hasithperera/APRS_tracker/data/aprs_v3_diagnostics/SCR01.PNG

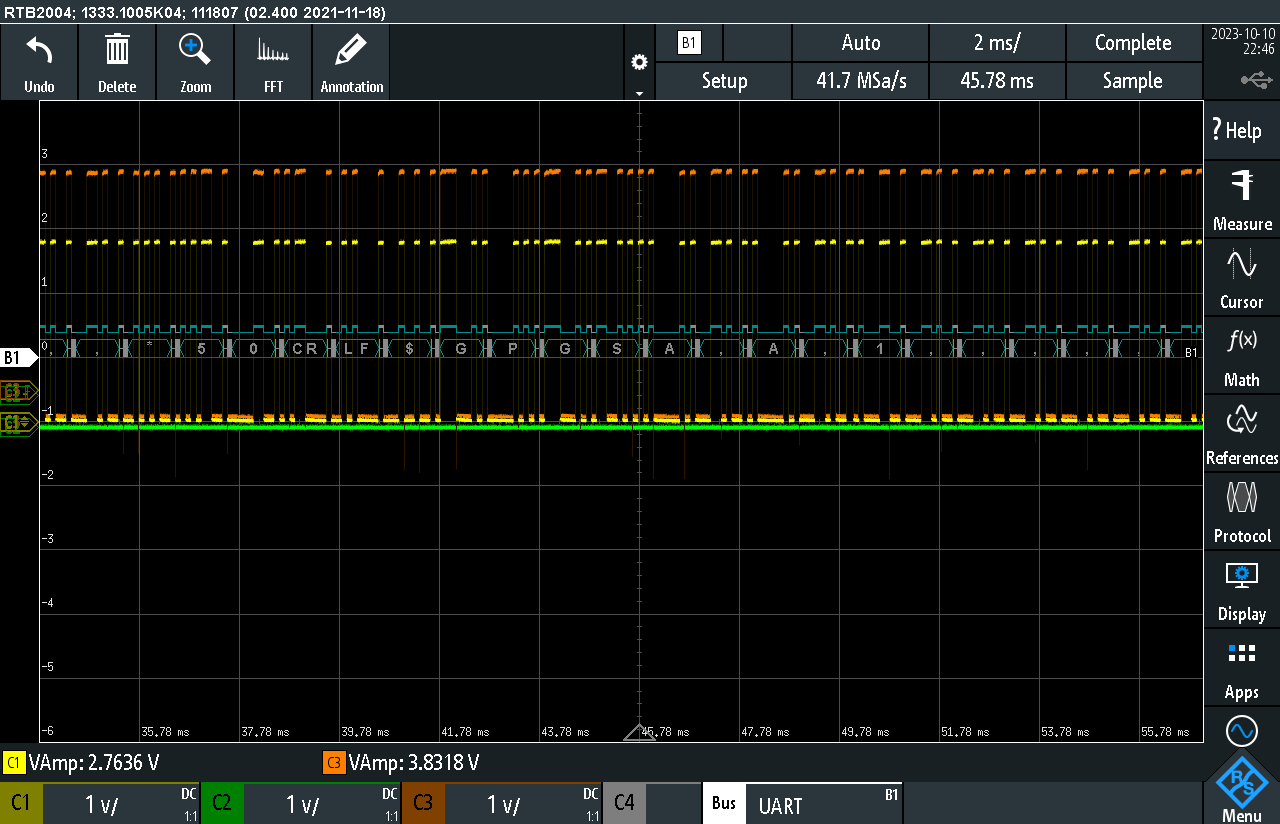
data/aprs_v3_diagnostics/SCR01.PNG
