hasithperera/APRS_tracker/data/DTMF/ALL0007/F0007TEK.BMP

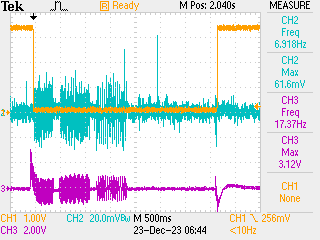
data/DTMF/ALL0007/F0007TEK.BMP
