hasithperera/APRS_tracker/doc/reports/res/aprs_PCB_v2.2.png

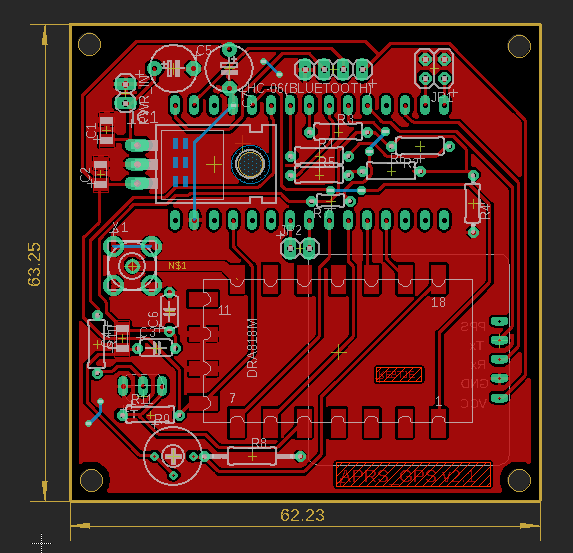
doc/reports/res/aprs_PCB_v2.2.png
