hasithperera/APRS_tracker/doc/reports/res/aprs_test.png

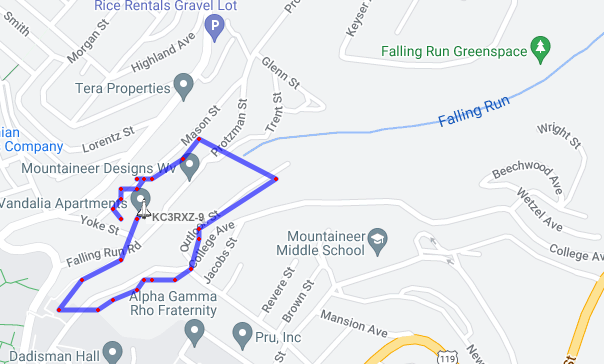
doc/reports/res/aprs_test.png
