hasithperera/APRS_tracker/data/aprs-data.py

#!/usr/bin/env python3
# -*- coding: utf-8 -*-
"""
Created on Mon Oct  2 08:38:33 2023
Author : Hasith Perera

"""

import numpy as np
import matplotlib.pyplot as plt

import pandas as pd

# indx = 363
# file = 'NEBP-2/aprsfi_export_KE8TJE-11_20230930_234754_20231001_234754.csv'
# file_MSU = './NEBP-2/flight-300234064701700-2023-10-01.csv'



indx = 519
file = 'HAB_launch-14_10_23/aprsfi_export_KE8TJE-11_20231013_205022_20231015_205022.csv';
file_MSU = './HAB_launch-14_10_23/flight-300234064701700-2023-10-14.csv'


df = pd.read_csv(file)

#0 - time
#2 - location data



df['data'] = df['comment'].str.split('=')
altitude = np.zeros([df.shape[0]])
for i in range(0,df.shape[0]):
    data = df['data'][i]
#    print(data)
#    
    if data[1]=='':
        altitude[i]=np.nan
        print(f'{i} !no alt')
        pass
    else:
        tmp_alt = float(data[1].split(' ')[0][0:-1])
        

        #print("{} float:{}".format((data[2]),tmp_alt))
        altitude[i] = tmp_alt
#        
df['alt'] = altitude
df['fixed_dt']=pd.to_datetime(df['time'], dayfirst=True,utc=True)



###################
### load MSU data
#
##plt.figure()

df_msu = pd.read_csv(file_MSU)
#
df_msu['fixed_dt']=pd.to_datetime(df_msu['datetime'], dayfirst=True)



#tx launch 300 

plt.plot((df_msu['fixed_dt']-df_msu['fixed_dt'][indx])/1e9,df_msu['altitude']/1000,'.-')

# plt.plot(df_msu['altitude']/1000,'.-')

#plt.xticks(np.arange(0, df_msu.shape[0], step=40),rotation='vertical')
plt.tight_layout()

plt.plot((df['fixed_dt']-df_msu['fixed_dt'][indx])/1e9,df['alt']/1000,'o-')
#plt.xticks(np.arange(0, df.shape[0], step=20),rotation='vertical')

plt.ylabel('Altitude (km)')
plt.xlabel('Time (s)')
plt.tight_layout()

# plt.legend(['Iridium','APRS'])


plt.legend(['iridium-1','aprs-1','iridium-2','aprs-2'])
#plt.show()
#
#
#
###
#
#file_fi = 'NEBP-2/aprsfi_data.dat'
#
#df2 = pd.DataFrame()
#
#with open(file_fi) as fp:
#    lines = fp.readlines()
#
#date_time = []
#alt = np.zeros([len(lines)])
#
#for i,line in enumerate(lines):
#    data_tmp = line.split('?')
#    val = str(data_tmp[0][0:-3])
#    print(val)
#    date_time.append(val+"-4:00")
#    
#    alt[i] = float(data_tmp[1].split("=")[-1][0:-2])
#
#
#df2['datetime'] = date_time;
#df2['alt'] = alt
#
#df2['fixed_dt'] = pd.to_datetime(df2['datetime'], dayfirst=True,utc=False)
#
#
#
#plt.plot(df2['fixed_dt'],df2['alt'],'o-')
#
#plt.xlabel('UTC time')
#plt.ylabel('Altitude (m)')
#plt.legend(['APRS Recovery','Iridium','APRS.fi'])
